jamesarbrown/Beolab-3500-Squeezebox/Stage3 - Replacement Crossfield PCB/Crossfield PCB Replacement/BC549.jpg

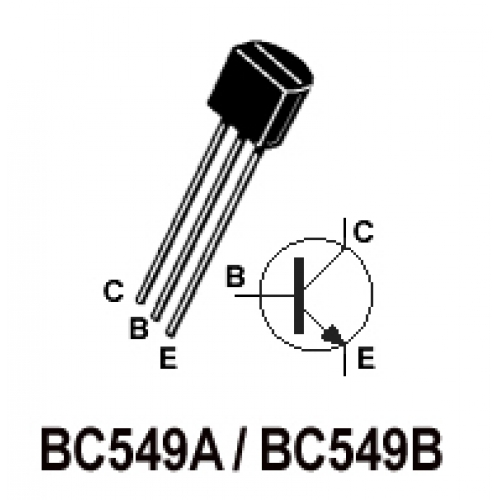
Stage3 - Replacement Crossfield PCB/Crossfield PCB Replacement/BC549.jpg
